wolfwood/navcaps/keycaps/trackpoint-3_5mm.scad

include <trackpoint-lp.scad>

function height_offset() = 3.5;
