wolfwood/navcaps/keycaps/trackpoint-3mm.scad

include <trackpoint-lp.scad>

function height_offset() = 3;
