wolfwood/navcaps/keycaps/trackpoint-slp.scad

include <trackpoint-lp.scad>

// Super Low Profile
function height_offset() = 4;
